Alex3404/Wakeup-Light-Dimmer/application/src/app/ui/mod.rs

// Include the Slint UI modules
#![allow(clippy::arithmetic_side_effects)]
slint::include_modules!();

// pub mod core;
// pub mod input;
pub mod slint_ui;

// pub(super) mod menus;
// pub use core::*;
